KaiBLI/EasyDABv2/KiCad Files/EasyDAB v2 Rev.6 Schematic.kicad_sch

## KiCad design KiCad Files/EasyDAB v2 Rev.6 Schematic.kicad_sch (2026-02-18)

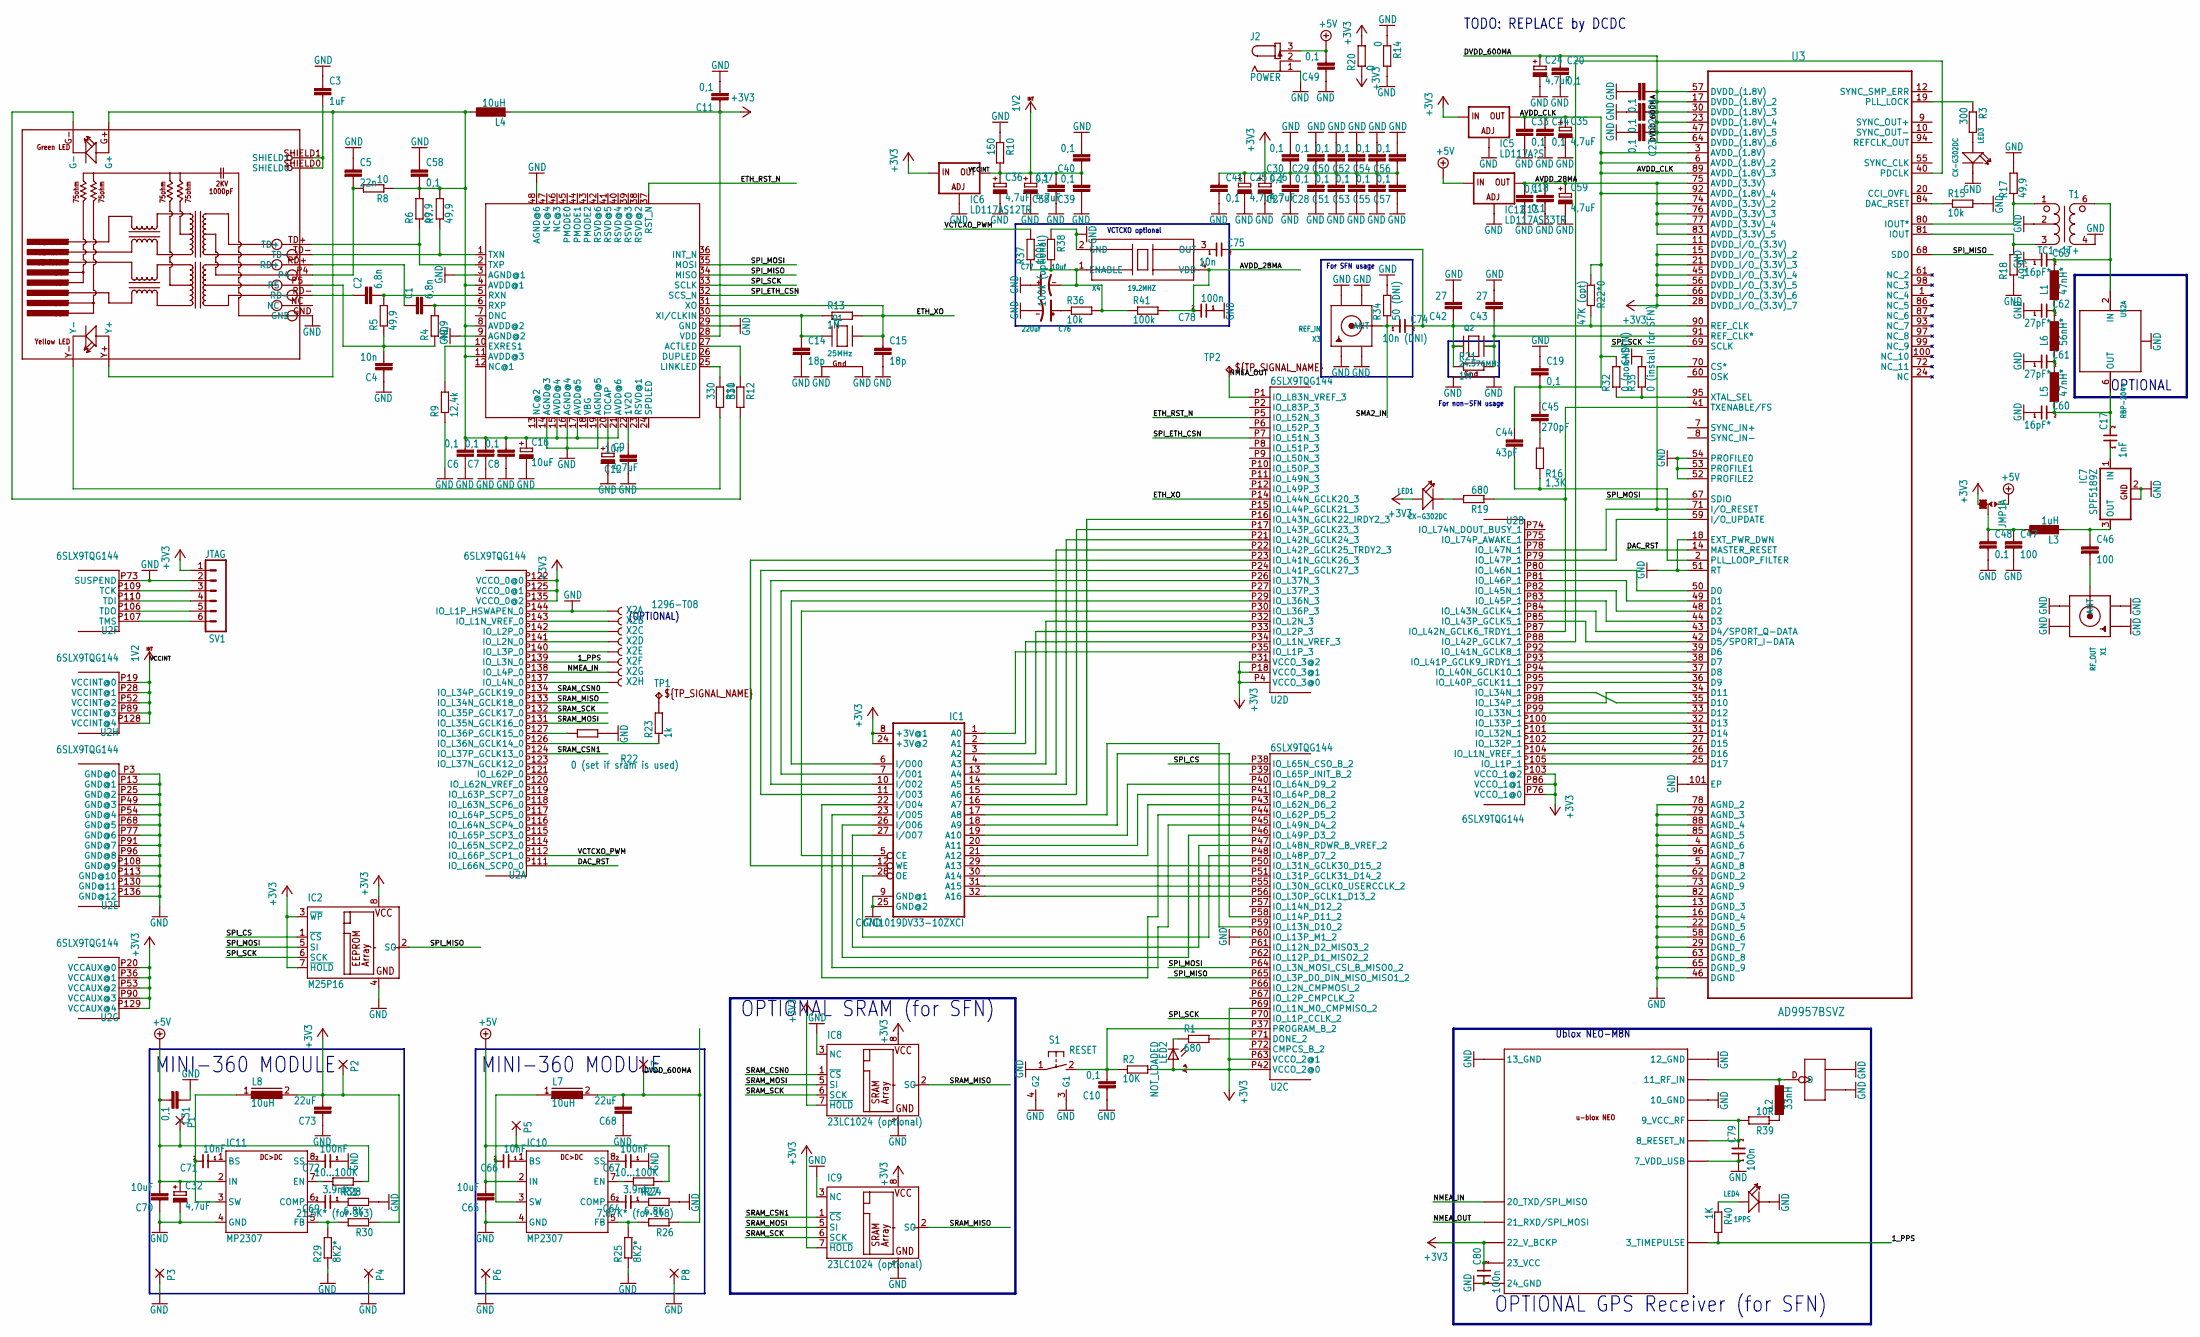
[picture p9: schematic EasyDAB v2 Rev.6 Schematic.kicad_sch]

Parts:
ANT1: U-FL; U-FL3P-SMD-2.6X2.6X1.0MM
C1, C2: 6,8n; C0805
C3: 1uF; C1206
C4, C12: 10n; C0805
C5: 22n; C0805
C6, C7, C8, C10, C11, C13, C18, C19, C20, C21, C22, C23, C27, C28, C29, C30, C31, C33, C34, C38, C39, C40, C41, C49, C50, C51, C52, C53, C54, C55, C56, C57, C58: 0,1; C0805
C9, C24, C25, C26, C32, C35, C36, C37, C59: 4,7uF; A_3216-18R
C14, C15: 18p; C0805
C16: 10uF; A_3216-18R
C17: 1nF; 0603
C42, C43: 27; C0805
C44: 43pF; C0805
C45: 270pF; C0805
C46, C47: 100; C0805
C48: 0.1; C0805
C60, C63: 16pF*; 0603
C61, C62: 27pF*; 0603
C64, C69: 3.9nF; 0603
C65, C70: 10uF; C1206
C66, C71: 10nF; 0603
C67, C72: 100nF; 0603
C68, C73: 22uF; C1206
C74: 10n (DNI); 0603
C75: 10n; 0603
C76: 220uf; AVX-D
C77: 10uf; AVX-A
C78, C79, C80: 100n; 0603
IC1: CY7C1019DV33-10ZXCI; TSOPII-32
IC2: M25P16; SO-08
IC5: LD117A?S; SOT223
IC6: LD117AS12TR; SOT223
IC7: SPF5189Z; SOT89
IC8, IC9: 23LC1024 (optional); SO-08
IC10, IC11: MP2307; SO8
IC12: LD117AS33TR; SOT223
J2: POWER; SPC4077
JMP1: 0R-JUMPA; A0R-JMP
L1, L5: 47nH*; INDC1608X95N
L2: 33nH; INDC1608X95N
L3: 1uH; L3216C
L4: 10uH; L3216C
L6: 56nH*; INDC1608X95N
L7, L8: 10uH; DR74
LED1, LED3: CX-G302DC; LED2-2.54-D3.0MM
LED2: NOT_LOADED; CHIPLED_1206
LED4: 1PPS; LED2-2.54-D3.0MM
P1, P2, P3, P4, P5, P6, P7, P8: 1,6/0,8; 1,6_0,8
Q1: 25MHz; NX3225
Q2: 24.576MHz; NX3225
R1, R19: 680; M0805
R2: 10K; M0805
R3: 300; M0805
R4, R5, R6, R7, R17, R18: 49,9; R0805
R8: 10; R0805
R9: 12,4k; R0805
R10: 150; R0805
R11, R12: 330; R0805
R13, R21: 1M; R0805
R14: 0; R0805
R15: 10k; R0805
R16: 1,3K; R0805
R20: 0; R1210
R22: 0 (set if sram is used); R0402
R22*0: 47K (opt); R0603
R23: 1k; R0603
R24, R28: 6.8K; R0603
R25, R29: 8K2*; R0603
R26: 7.87K* (for 1v8); R0603
R27, R31: 10...100K; R0603
R30: 21.5K* (for 3v3); R0603
R32: 0 (non-SFN); R0402
R33: 0 (install for SFN); R0402
R34: 50 (DNI); R0402
R36: 10k; R0603
R37, R41: 100k; R0603
R38: 100k (optional); R0603
R39: 10R; R0402
R40: 1K; R0402
RJ2: HR911105A
S1: RESET; B3F-31XX
SV1: JTAG; MA06-1
T1: TC1-1T+; AT224-3
TP1: PPS_IN; B1,27
TP2: UART_OUT; B1,27
U1: W5500
U2: 6SLX9TQG144; TQ144
U3: AD9957BSVZ; QFP50P1600X1600X120-101N
U$1: NEO-M8
U$2: RBP-204+; GP731
X1: RF_OUT; SMA90_DIP
X2: 1296-T08; 1296-08
X3: REF_IN; W5500_LX9_AD9957_SMA_EDGELAUNCH_UFL
X4: 19.2MHZ; X4-SMD-3.2X2.5X0.7MM

Connections:
1V2: C36.+, C37.+, C38.2, C39.2, C40.1, IC6.4 (OUT), R10.2, U2.P19 (VCCINT@0), U2.P28 (VCCINT@1), U2.P52 (VCCINT@2), U2.P89 (VCCINT@3), U2.P128 (VCCINT@4)
1_PPS: R40.2, U2.P139 (IO_L3N_0), U$1.3 (3_TIMEPULSE), X2.6
+3V3: C11.1, C25.+, C26.+, C27.2, C28.2, C29.1, C30.1, C41.1, C50.1, C51.2, C52.1, C53.2, C54.1, C55.2, C56.1, C57.2, C73.2, C80.2, IC1.8 (+3V@1), IC1.24 (+3V@2), IC2.3 (~WP), IC2.7 (~HOLD), IC2.8 (VCC), IC5.3 (IN), IC6.3 (IN), IC8.7 (~HOLD), IC8.8 (VCC), IC9.7 (~HOLD), IC9.8 (VCC), JMP1.3, L4.2, L8.2, LED1.A (+), LED2.A, P2.1, R2.2, R20.1, R20.2, R30.1, SV1.1, U1.28 (VDD), U2.P4 (VCCO_3@0), U2.P18 (VCCO_3@1), U2.P20 (VCCAUX@0), U2.P31 (VCCO_3@2), U2.P36 (VCCAUX@1), U2.P42 (VCCO_2@0), U2.P53 (VCCAUX@2), U2.P63 (VCCO_2@1), U2.P69 (IO_L1N_M0_CMPMISO_2), U2.P76 (VCCO_1@0), U2.P86 (VCCO_1@1), U2.P90 (VCCAUX@3), U2.P103 (VCCO_1@2), U2.P122 (VCCO_0@0), U2.P125 (VCCO_0@1), U2.P129 (VCCAUX@4), U2.P135 (VCCO_0@2), U3.11 (DVDD_I/O_(3.3V)), U3.15 (DVDD_I/O_(3.3V)_2), U3.21 (DVDD_I/O_(3.3V)_3), U3.28 (DVDD_I/O_(3.3V)_7), U3.45 (DVDD_I/O_(3.3V)_4), U3.56 (DVDD_I/O_(3.3V)_5), U3.66 (DVDD_I/O_(3.3V)_6), U$1.22 (22_V_BCKP), U$1.23 (23_VCC)
+5V: C31.2, C32.+, C49.2, C65.2, C70.2, IC10.2 (IN), IC11.2 (IN), IC12.3 (IN), J2.3, JMP1.1, P1.1, P5.1, R27.1, R31.1
AVDD_28MA: C13.2, C18.1, C59.+, C78.2, IC12.4 (OUT), R41.2, U3.74 (AVDD_(3.3V)_2), U3.75 (AVDD_(3.3V)), U3.76 (AVDD_(3.3V)_3), U3.77 (AVDD_(3.3V)_4), U3.83 (AVDD_(3.3V)_5), X4.4 (VDD)
AVDD_CLK: C19.2, C33.1, C35.+, C44.1, C45.1, IC5.4 (OUT), R22*0.1, R32.2, U3.3 (AVDD_(1.8V)), U3.6 (AVDD_(1.8V)_2), U3.89 (AVDD_(1.8V)_3), U3.92 (AVDD_(1.8V)_4)
DAC_RST: U2.P111 (IO_L66N_SCP0_0), U3.14 (MASTER_RESET)
DVDD_600MA: C20.1, C21.1, C22.1, C23.1, C24.+, C68.2, L7.2, P7.1, R26.1, U3.17 (DVDD_(1.8V)_2), U3.23 (DVDD_(1.8V)_4), U3.30 (DVDD_(1.8V)_3), U3.47 (DVDD_(1.8V)_5), U3.57 (DVDD_(1.8V)), U3.64 (DVDD_(1.8V)_6)
ETH_RST_N: U1.37 (RST_N), U2.P5 (IO_L52N_3)
ETH_XO: C15.1, Q1.3 (X2), R13.2, U1.31 (XO), U2.P14 (IO_L44N_GCLK20_3)
GND: ANT1.GND1, ANT1.GND2, C3.1, C4.1, C5.1, C6.1, C7.1, C8.1, C9.-, C10.1, C11.2, C12.1, C13.1, C14.2, C15.2, C16.-, C18.2, C19.1, C20.2, C21.2, C22.2, C23.2, C24.-, C25.-, C26.-, C27.1, C28.1, C29.2, C30.2, C31.1, C32.-, C33.2, C34.2, C35.-, C36.-, C37.-, C38.1, C39.1, C40.2, C41.2, C42.2, C43.2, C47.2, C48.2, C49.1, C50.2, C51.1, C52.2, C53.1, C54.2, C55.1, C56.2, C57.1, C58.1, C59.-, C60.1, C61.1, C62.1, C63.1, C65.1, C67.1, C68.1, C70.1, C72.1, C73.1, C76.-, C77.+, C78.1, C79.1, C80.1, IC1.9 (GND@1), IC1.25 (GND@2), IC2.4 (GND), IC5.1 (ADJ), IC6.1 (ADJ), IC7.2 (GND), IC7.2@1 (GND@1), IC8.3 (NC), IC8.4 (GND), IC9.3 (NC), IC9.4 (GND), IC10.4 (GND), IC11.4 (GND), IC12.1 (ADJ), J2.1, LED3.K (-), LED4.K (-), P3.1, P4.1, P6.1, P8.1, Q1.2 (G2), Q1.4 (G1), Q2.2 (G2), Q2.4 (G1), R9.1, R10.1, R14.1, R14.2, R15.2, R17.2, R18.1, R22.1, R24.2, R25.1, R28.2, R29.1, R33.2, R34.2, R38.1, RJ2.GND, S1.1, S1.3 (G1), S1.4 (G2), SV1.2, T1.2 (SCT), T1.4, U1.3 (AGND@1), U1.9 (AGND@2), U1.14 (AGND@3), U1.16 (AGND@4), U1.19 (AGND@5), U1.29 (GND), U1.48 (AGND@6), U2.P3 (GND@0), U2.P13 (GND@1), U2.P25 (GND@2), U2.P49 (GND@3), U2.P54 (GND@4), U2.P60 (IO_L13P_M1_2), U2.P68 (GND@5), U2.P73 (SUSPEND), U2.P77 (GND@6), U2.P91 (GND@7), U2.P96 (GND@8), U2.P108 (GND@9), U2.P113 (GND@10), U2.P130 (GND@11), U2.P136 (GND@12), U2.P144 (IO_L1P_HSWAPEN_0), U3.4 (AGND_6), U3.5 (AGND_8), U3.13 (DGND_3), U3.16 (DGND_4), U3.18 (EXT_PWR_DWN), U3.22 (DGND_5), U3.29 (DGND_7), U3.46 (DGND), U3.51 (RT), U3.52 (PROFILE2), U3.53 (PROFILE1), U3.54 (PROFILE0), U3.58 (DGND_6), U3.62 (DGND_2), U3.63 (DGND_8), U3.65 (DGND_9), U3.73 (AGND_9), U3.78 (AGND_2), U3.79 (AGND_3), U3.82 (AGND), U3.85 (AGND_5), U3.88 (AGND_4), U3.96 (AGND_7), U3.101 (EP), U$1.7 (7_VDD_USB), U$1.10 (10_GND), U$1.12 (12_GND), U$1.13 (13_GND), U$1.24 (24_GND), X1.GND1, X1.GND2, X1.GND3, X1.GND4, X2.1, X3.GND@1 (GND1), X3.GND@2 (GND2), X3.GND@3 (GND3), X3.GND@4 (GND4), X4.2 (GND)
NMEA_IN: U2.P138 (IO_L4P_0), U$1.20 (20_TXD/SPI_MISO), X2.7
NMEA_OUT: TP2.TP, U2.P1 (IO_L83N_VREF_3), U$1.21 (21_RXD/SPI_MOSI)
unnamed: ANT1.D, L2.2, U$1.11 (11_RF_IN)
unnamed: C1.1, RJ2.RD+
unnamed: C1.2, R4.2, U1.6 (RXP)
unnamed: C2.1, RJ2.RD-
unnamed: C2.2, R5.2, U1.5 (RXN)
unnamed: C3.2, RJ2.SHIELD0, RJ2.SHIELD1
unnamed: C4.2, R4.1, R5.1, RJ2.P5
unnamed: C5.2, R8.2, RJ2.P4
unnamed: C9.+, U1.20 (TOCAP)
unnamed: C10.2, R2.1, S1.2 (S), U2.P37 (PROGRAM_B_2)
unnamed: C12.2, U1.22 (1V2O)
unnamed: C14.1, Q1.1 (X1), R13.1, U1.30 (XI/CLKIN)
unnamed: C6.2, C7.2, C8.2, C16.+, C58.2, L4.1, R6.2, R7.2, R8.1, RJ2.G+, RJ2.Y+, U1.4 (AVDD@1), U1.8 (AVDD@2), U1.11 (AVDD@3), U1.15 (AVDD@4), U1.17 (AVDD@5), U1.21 (AVDD@6)
unnamed: C17.1, IC7.1 (IN)
unnamed: C17.2, C60.2, L5.1, U$2.6 (OUT)
unnamed: C42.1, C74.2, C75.2, Q2.1 (X1), R21.1, R22*0.2, U3.90 (REF_CLK)
unnamed: C43.1, Q2.3 (X2), R21.2, U3.91 (REF_CLK*)
unnamed: C44.2, R16.2, U3.2 (PLL_LOOP_FILTER)
unnamed: C45.2, R16.1
unnamed: C46.1, IC7.3 (OUT), L3.2
unnamed: C46.2, X1.ANTENNA (ANT)
unnamed: C47.1, C48.1, JMP1.2, L3.1
unnamed: C61.2, L5.2, L6.1
unnamed: C62.2, L1.1, L6.2
unnamed: C63.2, L1.2, T1.6 (PD), U$2.2 (IN)
unnamed: C64.1, R24.1
unnamed: C64.2, IC10.6 (COMP)
unnamed: C66.1, IC10.1 (BS)
unnamed: C66.2, IC10.3 (SW), L7.1
unnamed: C67.2, IC10.8 (SS)
unnamed: C69.1, R28.1
unnamed: C69.2, IC11.6 (COMP)
unnamed: C71.1, IC11.1 (BS)
unnamed: C71.2, IC11.3 (SW), L8.1
unnamed: C72.2, IC11.8 (SS)
unnamed: C75.1, X4.3 (OUT)
unnamed: C76.+, R36.1
unnamed: C77.-, R36.2, R37.1, R38.2, R41.1, X4.1 (ENABLE)
unnamed: C79.2, R39.2, U$1.8 (8_RESET_N), U$1.9 (9_VCC_RF)
unnamed: IC1.1 (A0), U2.P35 (IO_L1P_3)
unnamed: IC1.2 (A1), U2.P34 (IO_L1N_VREF_3)
unnamed: IC1.3 (A2), U2.P33 (IO_L2P_3)
unnamed: IC1.4 (A3), U2.P32 (IO_L2N_3)
unnamed: IC1.5 (CE), U2.P30 (IO_L36P_3)
unnamed: IC1.6 (I/O00), U2.P29 (IO_L36N_3)
unnamed: IC1.7 (I/O01), U2.P27 (IO_L37P_3)
unnamed: IC1.10 (I/O02), U2.P26 (IO_L37N_3)
unnamed: IC1.11 (I/O03), U2.P24 (IO_L41P_GCLK27_3)
unnamed: IC1.12 (WE), U2.P23 (IO_L41N_GCLK26_3)
unnamed: IC1.13 (A4), U2.P22 (IO_L42P_GCLK25_TRDY2_3)
unnamed: IC1.14 (A5), U2.P21 (IO_L42N_GCLK24_3)
unnamed: IC1.15 (A6), U2.P17 (IO_L43P_GCLK23_3)
unnamed: IC1.16 (A7), U2.P16 (IO_L43N_GCLK22_IRDY2_3)
unnamed: IC1.17 (A8), U2.P59 (IO_L13N_D10_2)
unnamed: IC1.18 (A9), U2.P58 (IO_L14P_D11_2)
unnamed: IC1.19 (A10), U2.P40 (IO_L64N_D9_2)
unnamed: IC1.20 (A11), U2.P41 (IO_L64P_D8_2)
unnamed: IC1.21 (A12), U2.P43 (IO_L62N_D6_2)
unnamed: IC1.22 (I/O04), U2.P44 (IO_L62P_D5_2)
unnamed: IC1.23 (I/O05), U2.P45 (IO_L49N_D4_2)
unnamed: IC1.26 (I/O06), U2.P46 (IO_L49P_D3_2)
unnamed: IC1.27 (I/O07), U2.P47 (IO_L48N_RDWR_B_VREF_2)
unnamed: IC1.28 (OE), U2.P48 (IO_L48P_D7_2)
unnamed: IC1.29 (A13), U2.P50 (IO_L31N_GCLK30_D15_2)
unnamed: IC1.30 (A14), U2.P51 (IO_L31P_GCLK31_D14_2)
unnamed: IC1.31 (A15), U2.P55 (IO_L30N_GCLK0_USERCCLK_2)
unnamed: IC1.32 (A16), U2.P56 (IO_L30P_GCLK1_D13_2)
unnamed: IC10.5 (FB), R25.2, R26.2
unnamed: IC10.7 (EN), R27.2
unnamed: IC11.5 (FB), R29.2, R30.2
unnamed: IC11.7 (EN), R31.2
unnamed: L2.1, R39.1
unnamed: LED1.K (-), R19.2
unnamed: LED2.C, R1.1
unnamed: LED3.A (+), R3.2
unnamed: LED4.A (+), R40.1
unnamed: R1.2, U2.P71 (DONE_2)
unnamed: R3.1, U3.19 (PLL_LOCK)
unnamed: R6.1, RJ2.TD+, U1.2 (TXP)
unnamed: R7.1, RJ2.TD-, U1.1 (TXN)
unnamed: R9.2, U1.10 (EXRES1)
unnamed: R11.1, U1.25 (LINKLED)
unnamed: R11.2, RJ2.Y-
unnamed: R12.1, U1.27 (ACTLED)
unnamed: R12.2, RJ2.G-
unnamed: R15.1, U3.84 (DAC_RSET)
unnamed: R17.1, T1.1 (SD), U3.80 (IOUT*)
unnamed: R18.2, T1.3 (S), U3.81 (IOUT)
unnamed: R19.1, U2.P87 (IO_L42N_GCLK6_TRDY1_1), U3.41 (TXENABLE/FS)
unnamed: R22.2, U2.P127 (IO_L36P_GCLK15_0)
unnamed: R23.1, U2.P126 (IO_L36N_GCLK14_0)
unnamed: R23.2, TP1.TP
unnamed: R32.1, R33.1, U3.95 (XTAL_SEL)
unnamed: SV1.3, U2.P109 (TCK)
unnamed: SV1.4, U2.P110 (TDI)
unnamed: SV1.5, U2.P106 (TDO)
unnamed: SV1.6, U2.P107 (TMS)
unnamed: U2.P78 (IO_L47N_1), U3.70 (CS*), U3.71 (I/O_RESET)
unnamed: U2.P79 (IO_L47P_1), U3.59 (I/O_UPDATE)
unnamed: U2.P80 (IO_L46N_1), U3.50 (D0)
unnamed: U2.P81 (IO_L46P_1), U3.49 (D1)
unnamed: U2.P82 (IO_L45N_1), U3.48 (D2)
unnamed: U2.P83 (IO_L45P_1), U3.44 (D3)
unnamed: U2.P84 (IO_L43N_GCLK4_1), U3.43 (D4/SPORT_Q-DATA)
unnamed: U2.P85 (IO_L43P_GCLK5_1), U3.42 (D5/SPORT_I-DATA)
unnamed: U2.P88 (IO_L42P_GCLK7_1), U3.40 (PDCLK)
unnamed: U2.P92 (IO_L41N_GCLK8_1), U3.39 (D6)
unnamed: U2.P93 (IO_L41P_GCLK9_IRDY1_1), U3.38 (D7)
unnamed: U2.P94 (IO_L40N_GCLK10_1), U3.37 (D8)
unnamed: U2.P95 (IO_L40P_GCLK11_1), U3.36 (D9)
unnamed: U2.P97 (IO_L34N_1), U3.35 (D10)
unnamed: U2.P98 (IO_L34P_1), U3.34 (D11)
unnamed: U2.P99 (IO_L33N_1), U3.33 (D12)
unnamed: U2.P100 (IO_L33P_1), U3.32 (D13)
unnamed: U2.P101 (IO_L32N_1), U3.31 (D14)
unnamed: U2.P102 (IO_L32P_1), U3.27 (D15)
unnamed: U2.P104 (IO_L1N_VREF_1), U3.26 (D16)
unnamed: U2.P105 (IO_L1P_1), U3.25 (D17)
unnamed: U2.P137 (IO_L4N_0), X2.8
unnamed: U2.P140 (IO_L3P_0), X2.5
unnamed: U2.P141 (IO_L2N_0), X2.4
unnamed: U2.P142 (IO_L2P_0), X2.3
unnamed: U2.P143 (IO_L1N_VREF_0), X2.2
SMA2_IN: C74.1, R34.1, X3.P (ANT)
SPI_CS: IC2.1 (~CS), U2.P38 (IO_L65N_CSO_B_2)
SPI_ETH_CSN: U1.32 (SCS_N), U2.P7 (IO_L51N_3)
SPI_MISO: IC2.2 (SO), U1.34 (MISO), U2.P65 (IO_L3P_D0_DIN_MISO_MISO1_2), U3.68 (SDO)
SPI_MOSI: IC2.5 (SI), U1.35 (MOSI), U2.P64 (IO_L3N_MOSI_CSI_B_MISO0_2), U3.67 (SDIO)
SPI_SCK: IC2.6 (SCK), U1.33 (SCLK), U2.P70 (IO_L1P_CCLK_2), U3.69 (SCLK)
SRAM_CSN0: IC8.1 (~CS), U2.P134 (IO_L34P_GCLK19_0)
SRAM_CSN1: IC9.1 (~CS), U2.P124 (IO_L37P_GCLK13_0)
SRAM_MISO: IC8.2 (SO), IC9.2 (SO), U2.P133 (IO_L34N_GCLK18_0)
SRAM_MOSI: IC8.5 (SI), IC9.5 (SI), U2.P131 (IO_L35N_GCLK16_0)
SRAM_SCK: IC8.6 (SCK), IC9.6 (SCK), U2.P132 (IO_L35P_GCLK17_0)
VCTCXO_PWM: R37.2, U2.P112 (IO_L66P_SCP1_0)

Notes on the sheet:
MINI-360 MODULE
Ublox NEO-M8N
OPTIONAL GPS Receiver (for SFN)
VCTCXO optional
TODO: REPLACE by DCDC
For non-SFN usage
(OPTIONAL)
OPTIONAL SRAM (for SFN)
OPTIONAL
For SFN usage
